eclipse-kuksa/kuksa-hardware/hw_doc/img/CANOPi_3D_FullAssembly_Iso_Bot.PNG

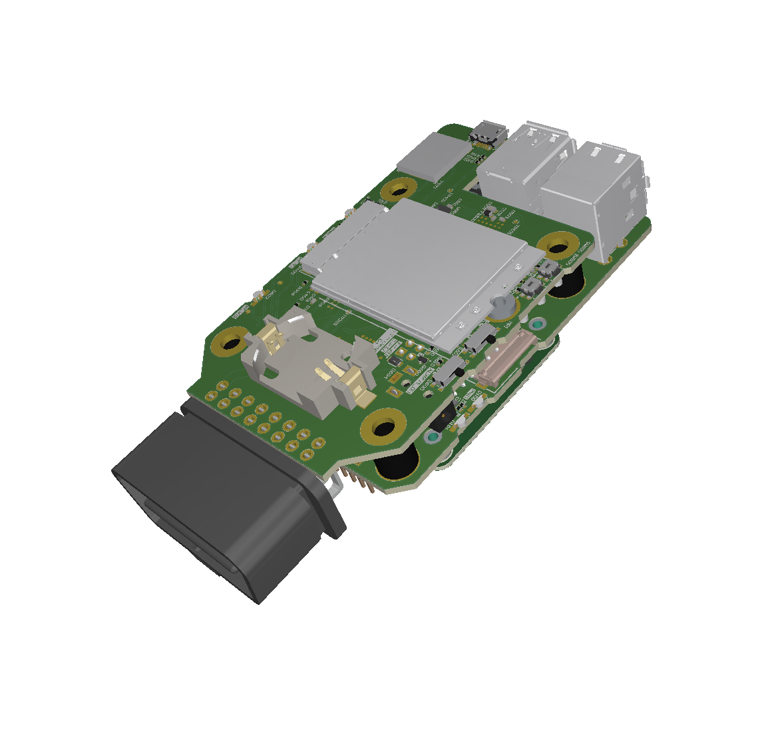
hw_doc/img/CANOPi_3D_FullAssembly_Iso_Bot.PNG
