eclipse-kuksa/kuksa-hardware/hw_doc/img/CANOPi_3D_FullAssembly_Top.PNG

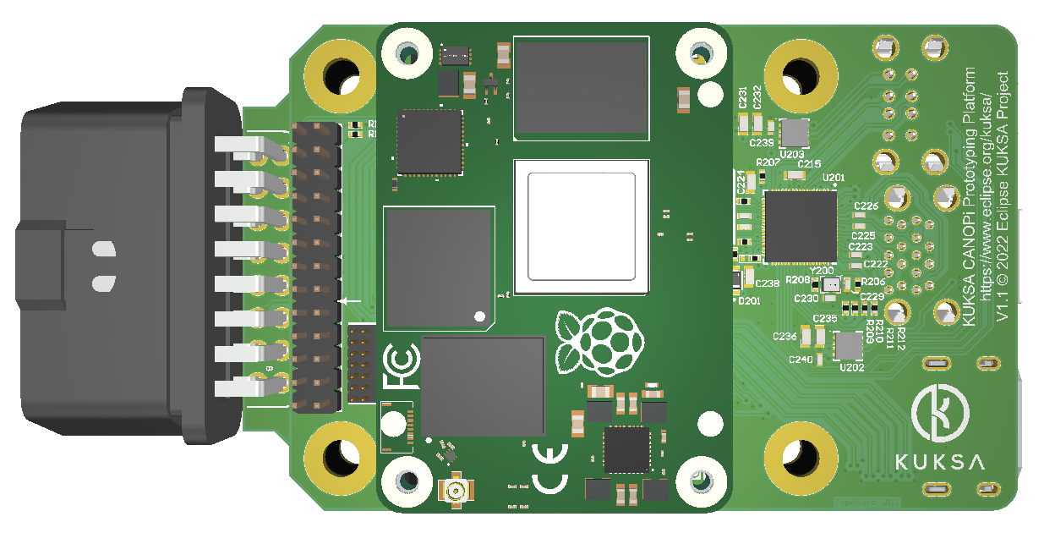
hw_doc/img/CANOPi_3D_FullAssembly_Top.PNG
